MOSH-Insa-Toulouse/2024-2025-4GP-Tajan-Benos/Capteur_graphique/Modele 3D/Encodeur-rotatif/Screen Shot 2022-12-16 at 3.19.57 PM.png

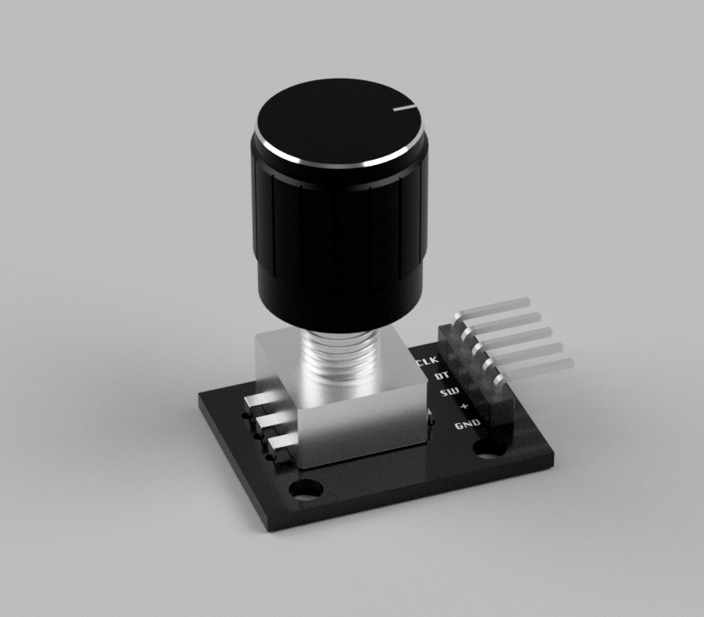
Capteur_graphique/Modele 3D/Encodeur-rotatif/Screen Shot 2022-12-16 at 3.19.57 PM.png
