MOSH-Insa-Toulouse/2024-2025-4GP-Tajan-Benos/Capteur_graphique/Modele 3D/hc-05-bluetooth-module-4.snapshot.3/Capture.JPG

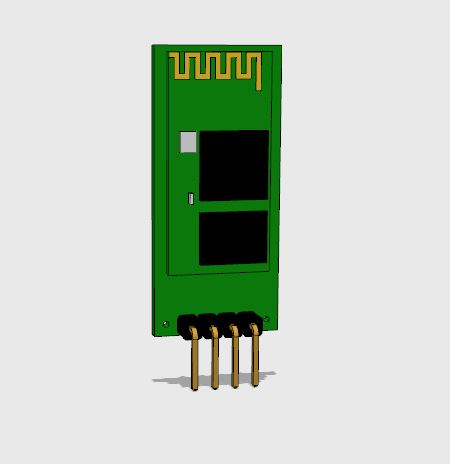
Capteur_graphique/Modele 3D/hc-05-bluetooth-module-4.snapshot.3/Capture.JPG
