MOSH-Insa-Toulouse/2024-2025-4GP-Tajan-Benos/Capteur_graphique/Modele 3D/OLED/Pantalla OLED 0.96'' 128x64 trasera.png

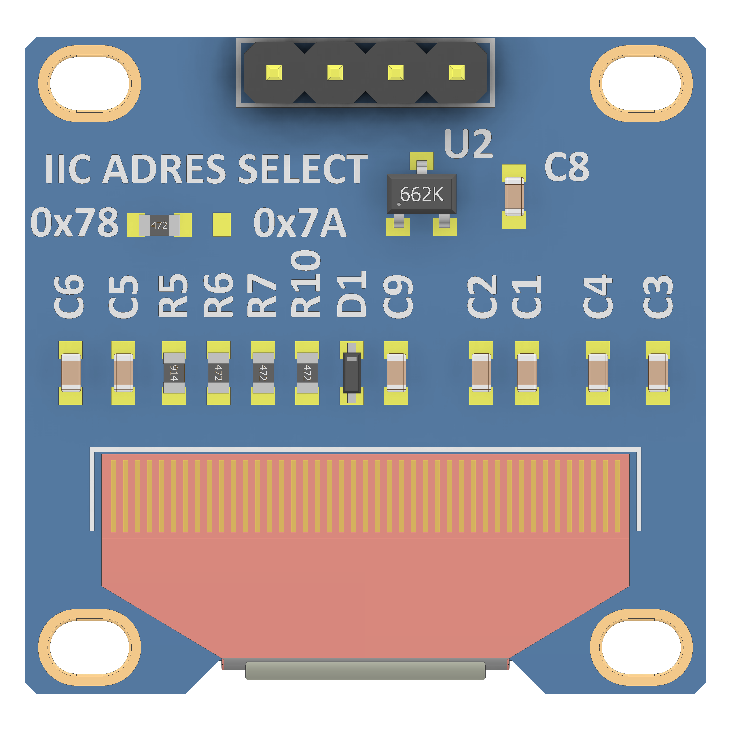
Capteur_graphique/Modele 3D/OLED/Pantalla OLED 0.96'' 128x64 trasera.png
