MOSH-Insa-Toulouse/2024-2025-4GP-Tajan-Benos/Image/Empreinte/Empreinte_Potentiomètre_digital.png

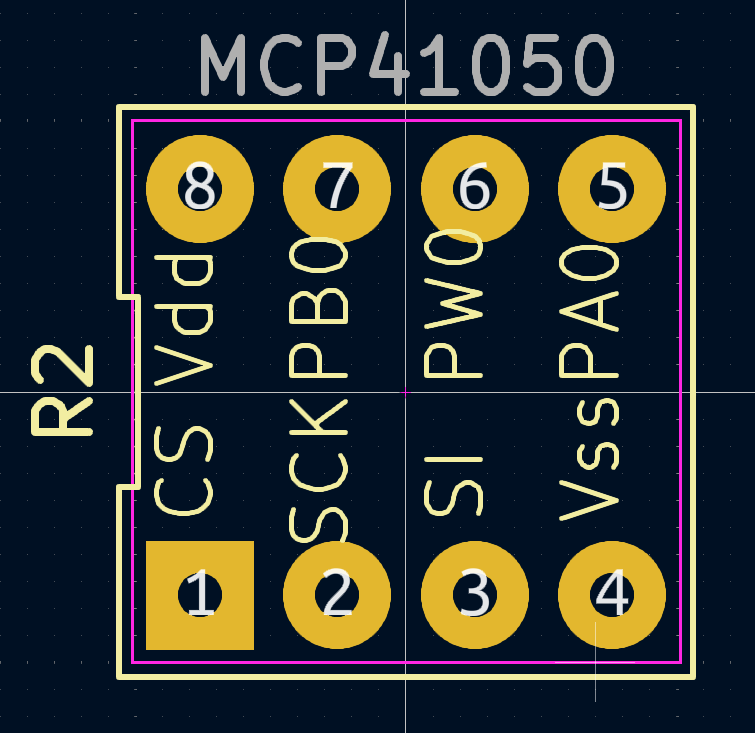
Image/Empreinte/Empreinte_Potentiomètre_digital.png
