MOSH-Insa-Toulouse/2024-2025-4GP-Tajan-Benos/Image/Symbole/Symbole_Bluetoth.png

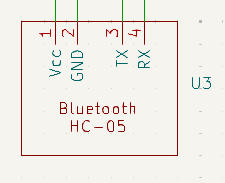
Image/Symbole/Symbole_Bluetoth.png
